Peter010103/CUR_Gripper/catkin_ws/src/gripperv4/assets/pitch_mount1.stl

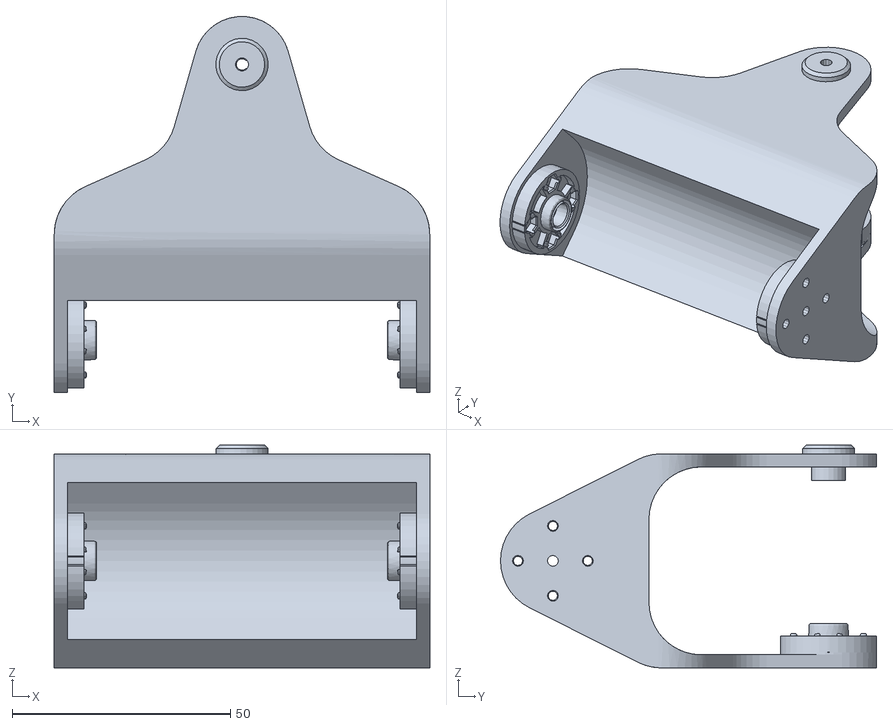
[picture p17: CAD file, 2020-09-12]
catkin_ws/src/gripperv4/assets/pitch_mount1.stl
86.0 x 86.1 x 51.0
