Peter010103/CUR_Gripper/assets/STL/l_link1_top.stl

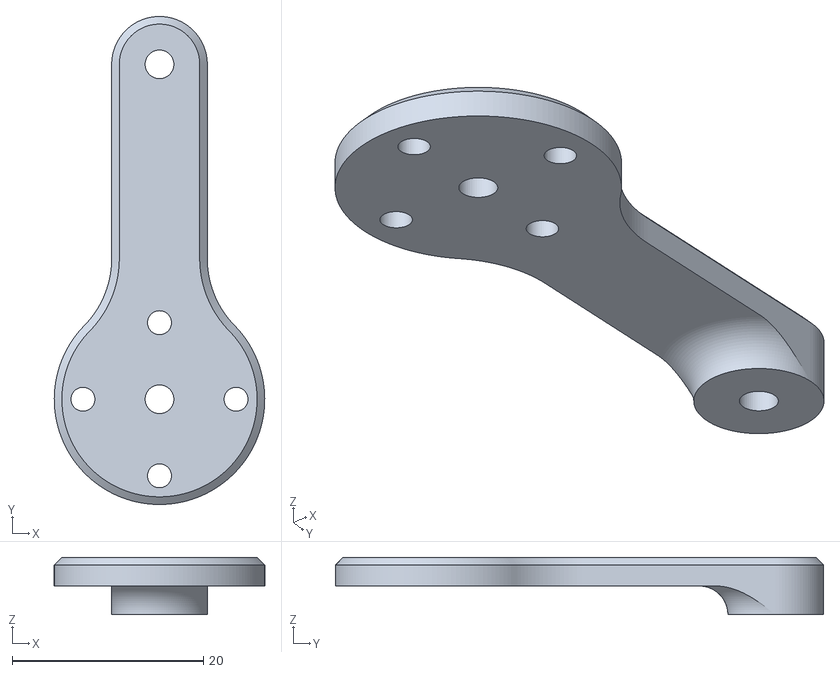
[picture p18: CAD file, 2020-09-12]
assets/STL/l_link1_top.stl
22.0 x 51.0 x 6.00
