Peter010103/CUR_Gripper/gripperv4_description/meshes/L_Body_1.stl

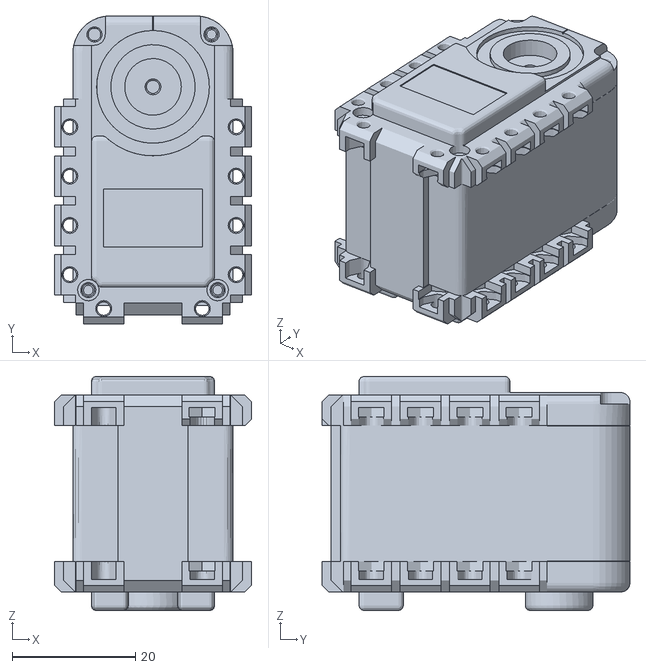
[picture p19: CAD file, 2020-09-07]
gripperv4_description/meshes/L_Body_1.stl
32.0 x 50.0 x 38.0
