Peter010103/CUR_Gripper/assets/STL/r_link1_bushing.stl

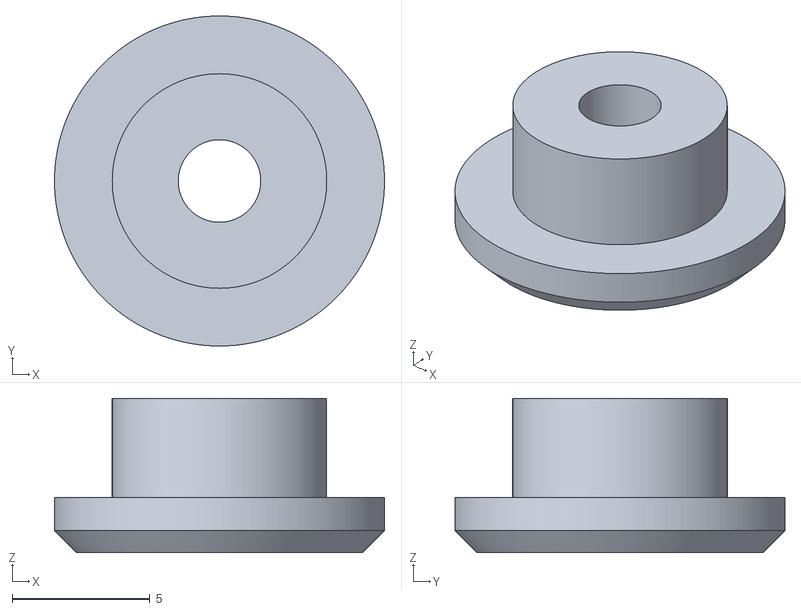
[picture p20: CAD file, 2020-09-12]
assets/STL/r_link1_bushing.stl
12.0 x 12.0 x 5.60
