Peter010103/CUR_Gripper/gripperv4_description/meshes/L_Link3_1.stl

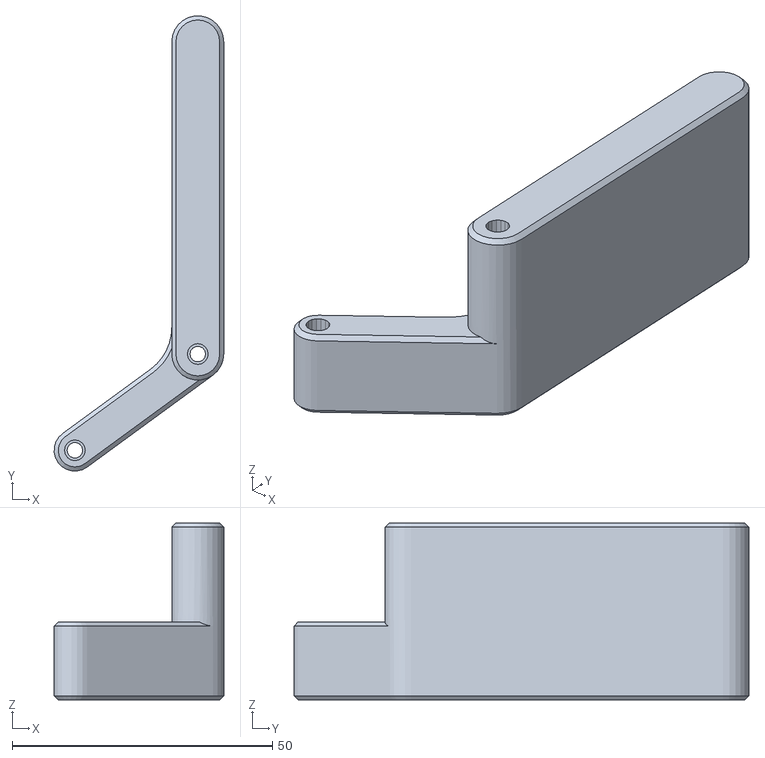
[picture p21: CAD file, 2020-09-07]
gripperv4_description/meshes/L_Link3_1.stl
32.6 x 87.4 x 34.0
