Peter010103/CUR_Gripper/catkin_ws/src/gripperv4/assets/roll2yaw_mount1.stl

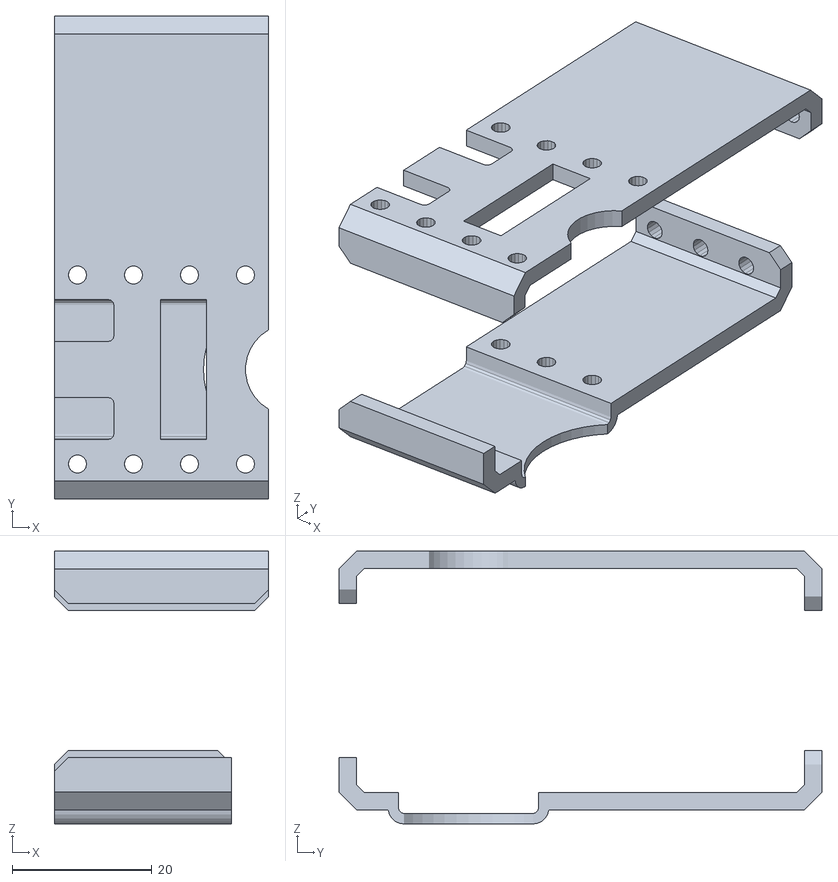
[picture p22: CAD file, 2020-09-07]
catkin_ws/src/gripperv4/assets/roll2yaw_mount1.stl
30.6 x 69.0 x 39.0
